sparkfun/SparkFun_RTK_Facet/Labels/SMA Cover - Blank/RTK Facet - SMA cover - Blank r2.pdf

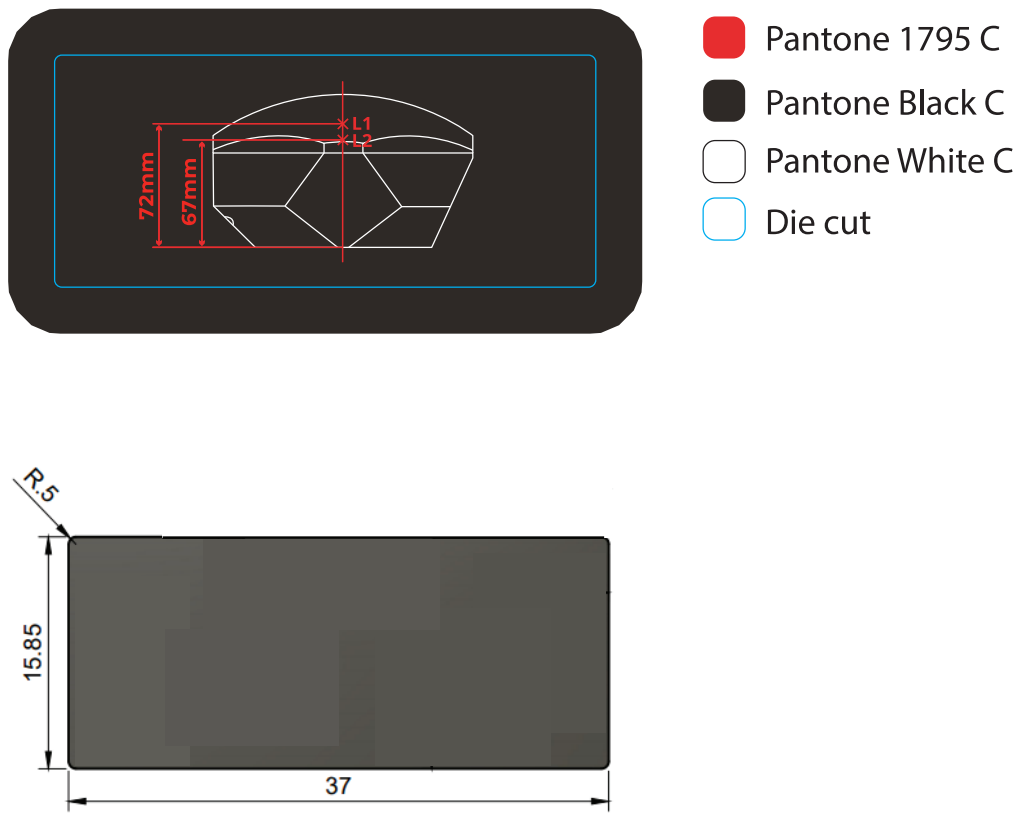
[picture p37: page 1]
