sparkfun/SparkFun_RTK_Facet/Labels/SMA Cover - Blank/RTK Facet - SMA cover - Blank LBand r1.pdf

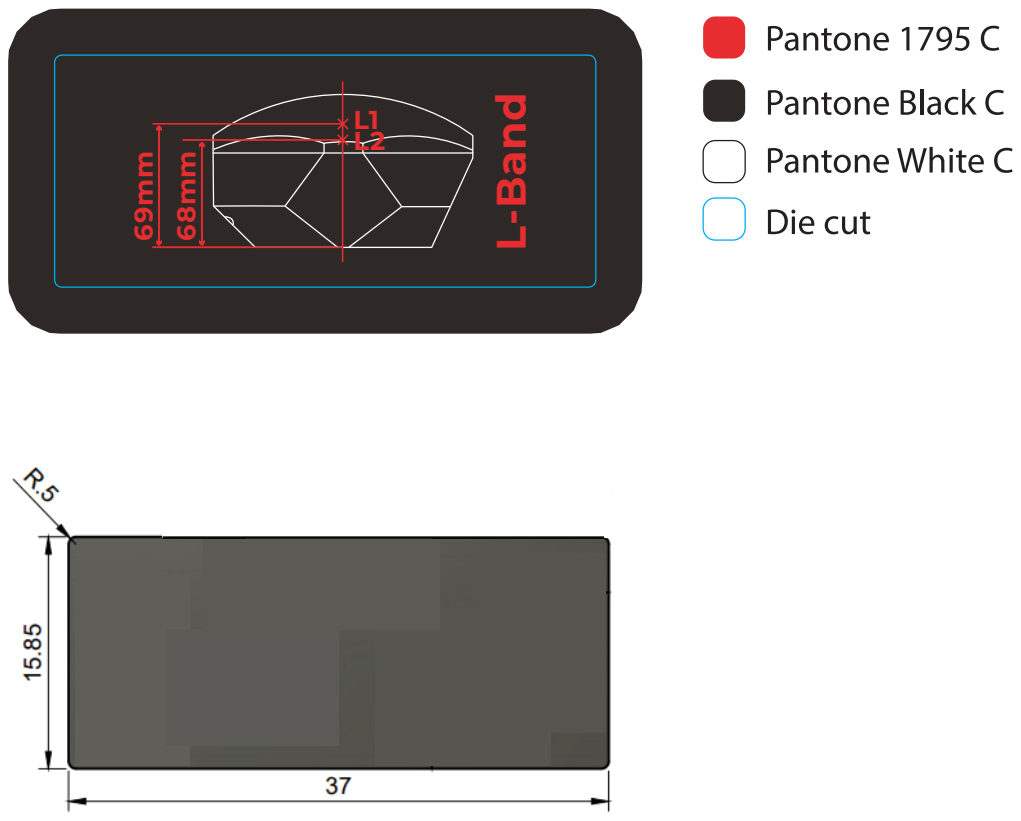
[picture p38: page 1]
L-Band
