sparkfun/SparkFun_RTK_Facet/Labels/SMA Cover - 915MHz/RTK Facet 915MHz Label (r1).pdf

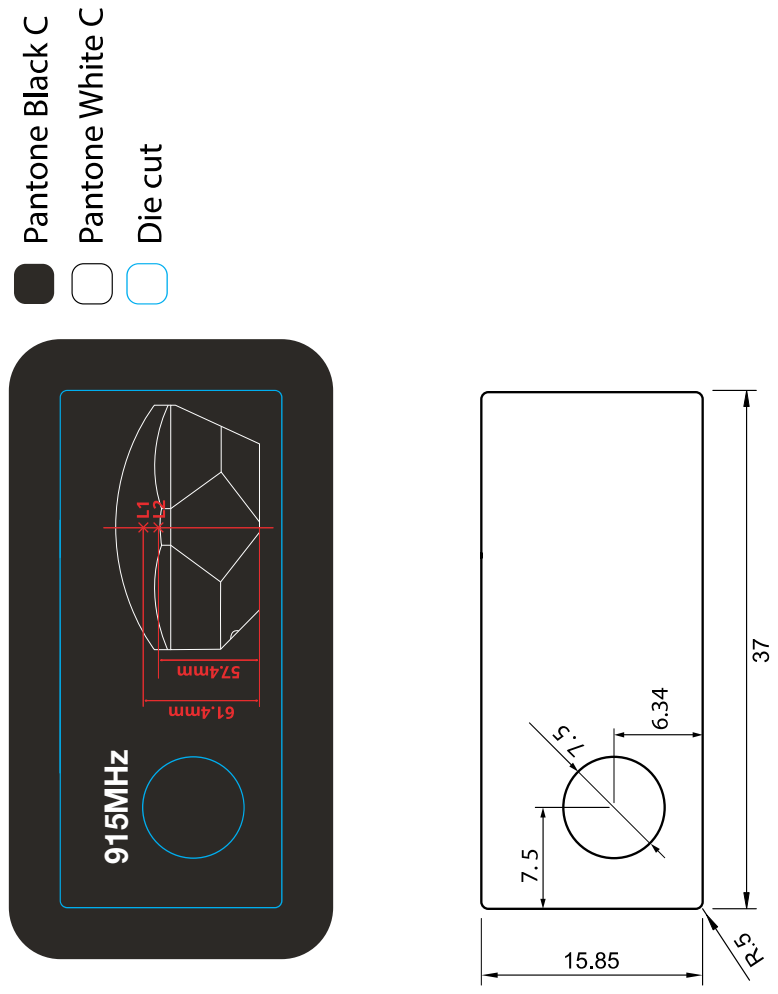
[picture p39: page 1]
915MHz
