sparkfun/SparkFun_RTK_Facet/Labels/SMA Cover - LTE/RTK Facet LTE Label.pdf

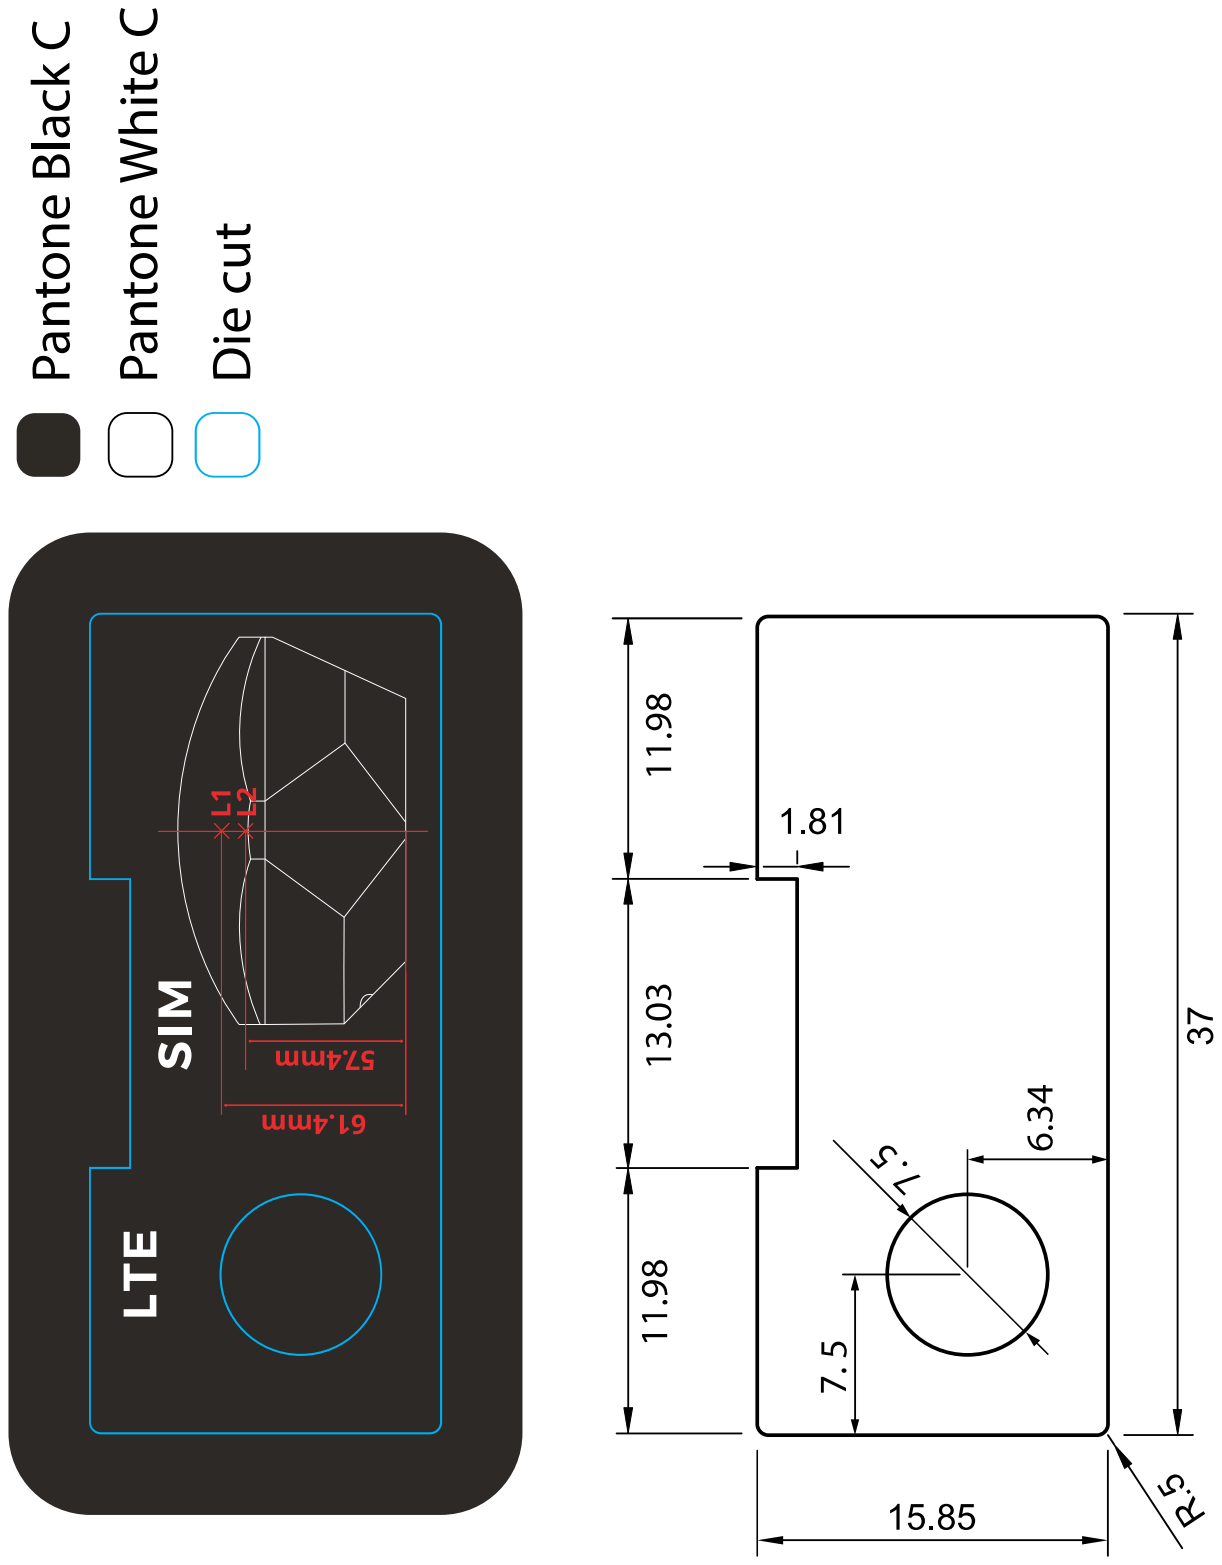
[picture p40: page 1]
