sparkfun/SparkFun_RTK_Facet/Labels/Display/RTK Facet Labels - All Outlines r2.pdf

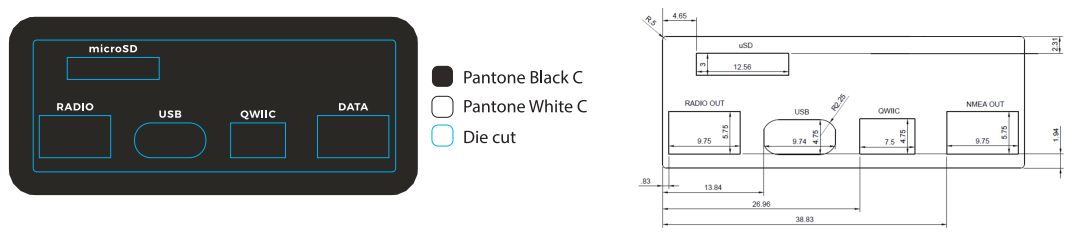
[picture p41: page 1]

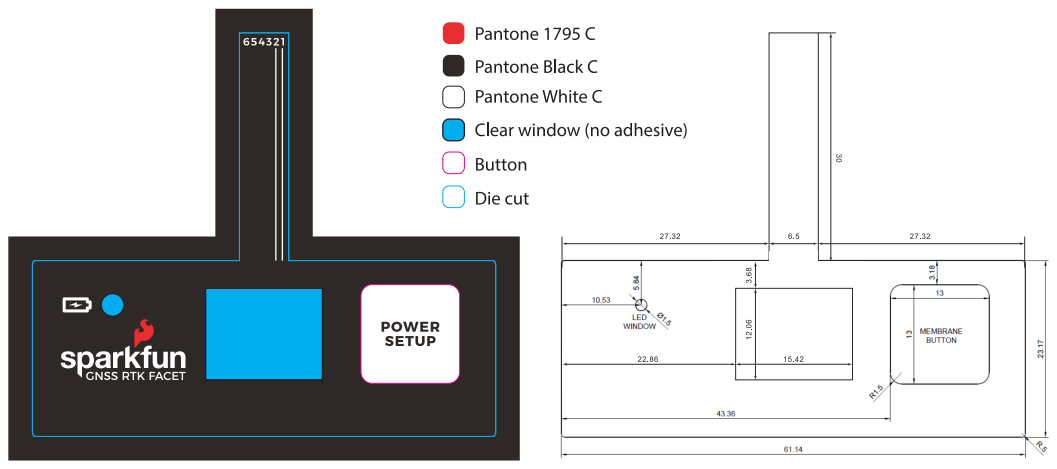
[picture p42: page 2]

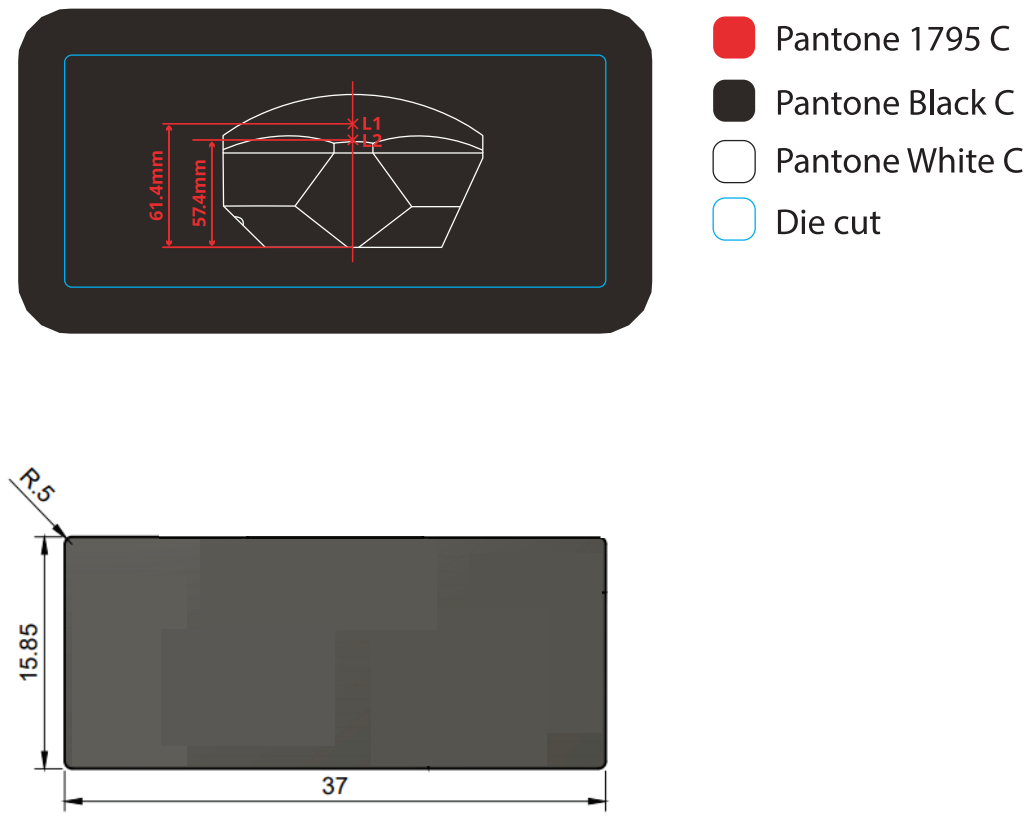
[picture p43: page 4]

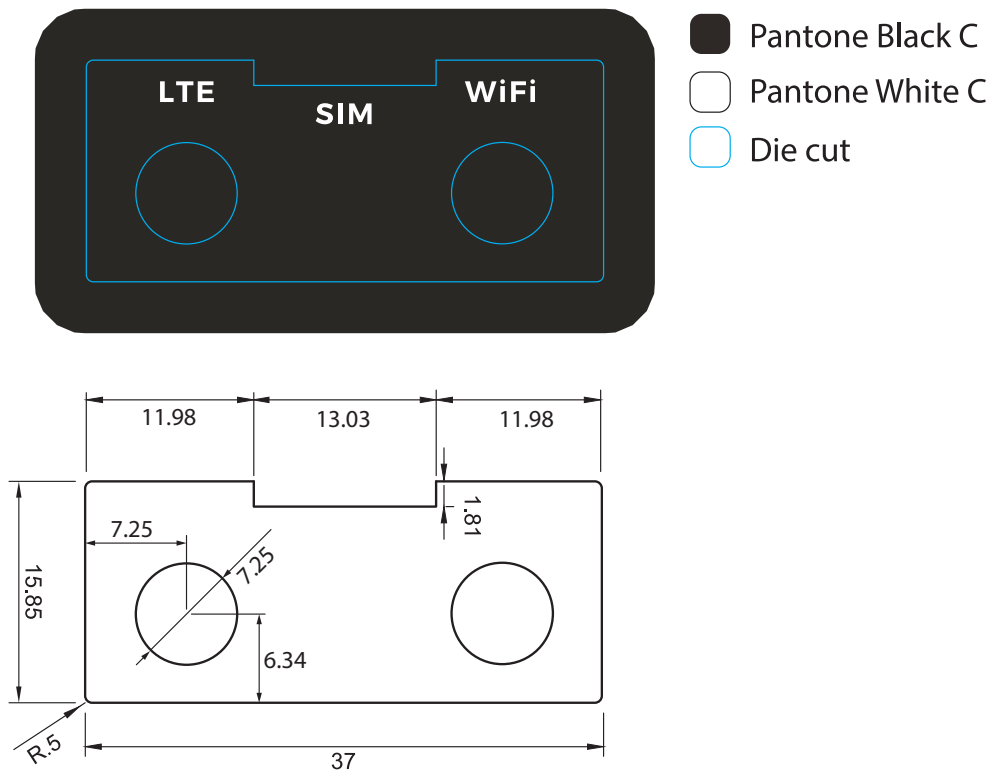
[picture p44: page 5]

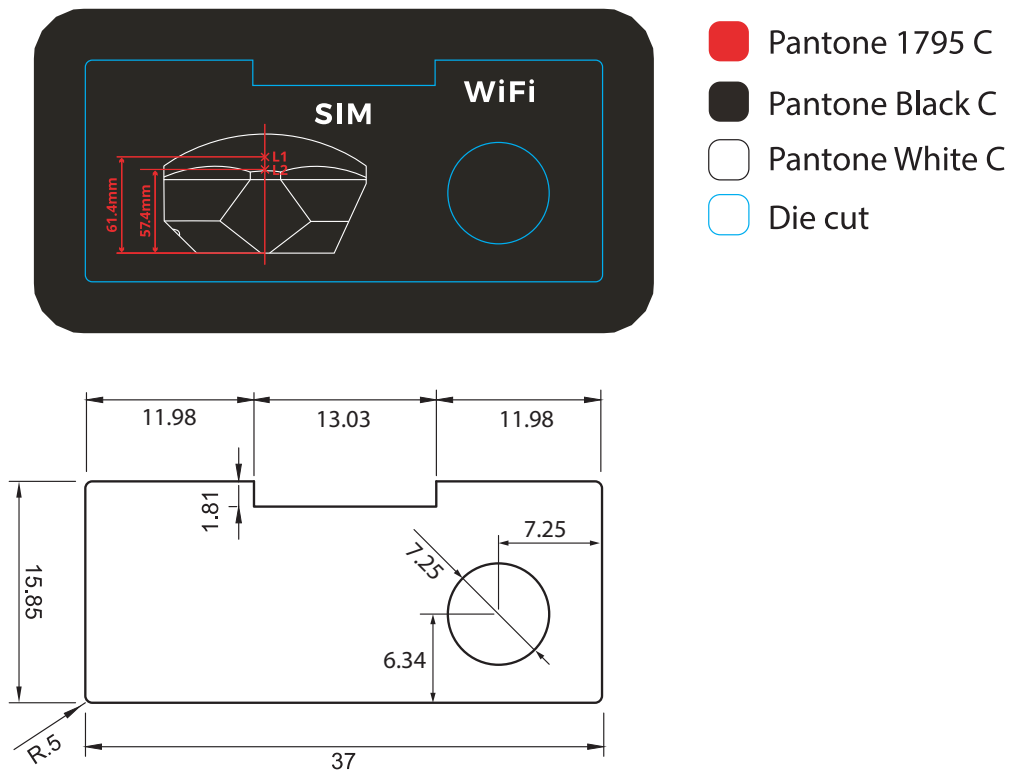
[picture p45: page 6]

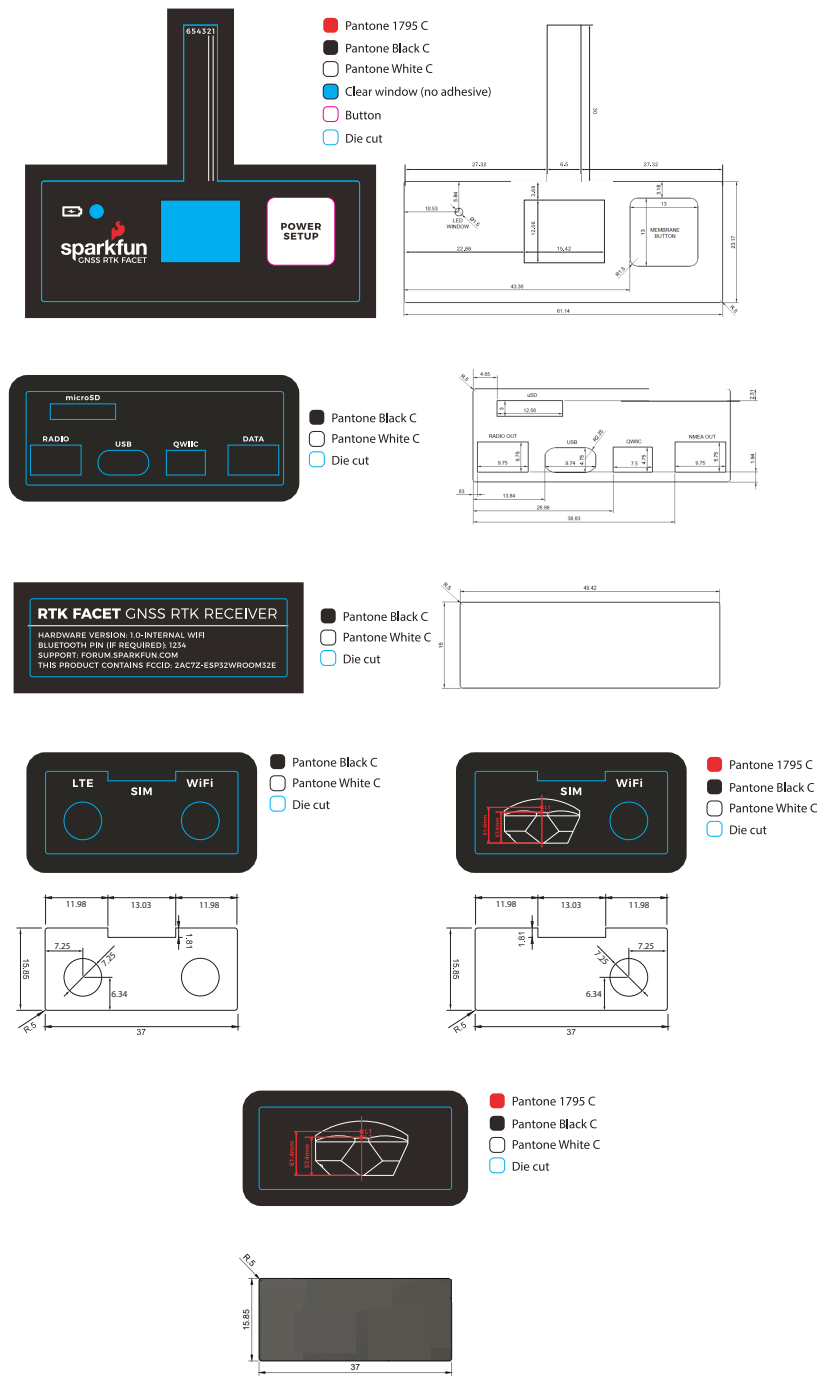
[picture p46: page 7]
