sparkfun/SparkFun_RTK_Facet/Labels/SMA Cover - WiFi+LTE/RTK Facet LTE+WiFi Label r2.pdf

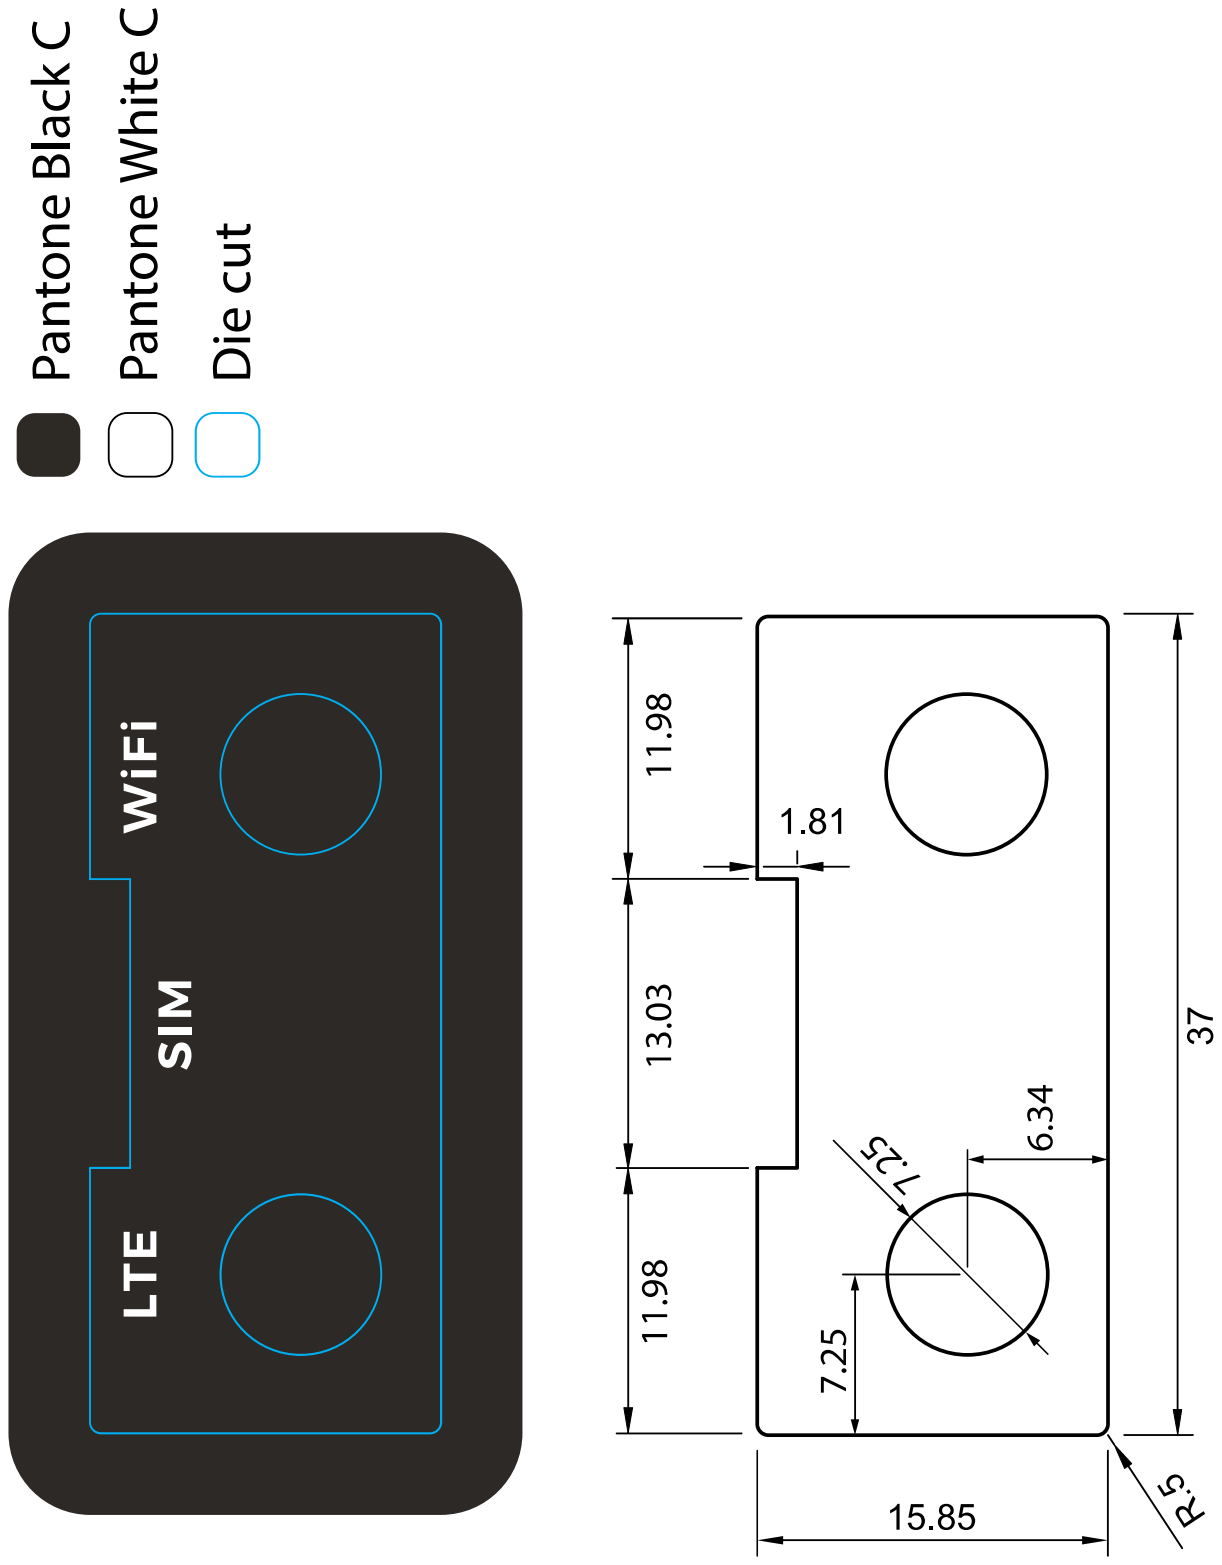
[picture p47: page 1]
