sparkfun/SparkFun_RTK_Facet/Labels/Display/RTK Facet - All Outlines r1.pdf

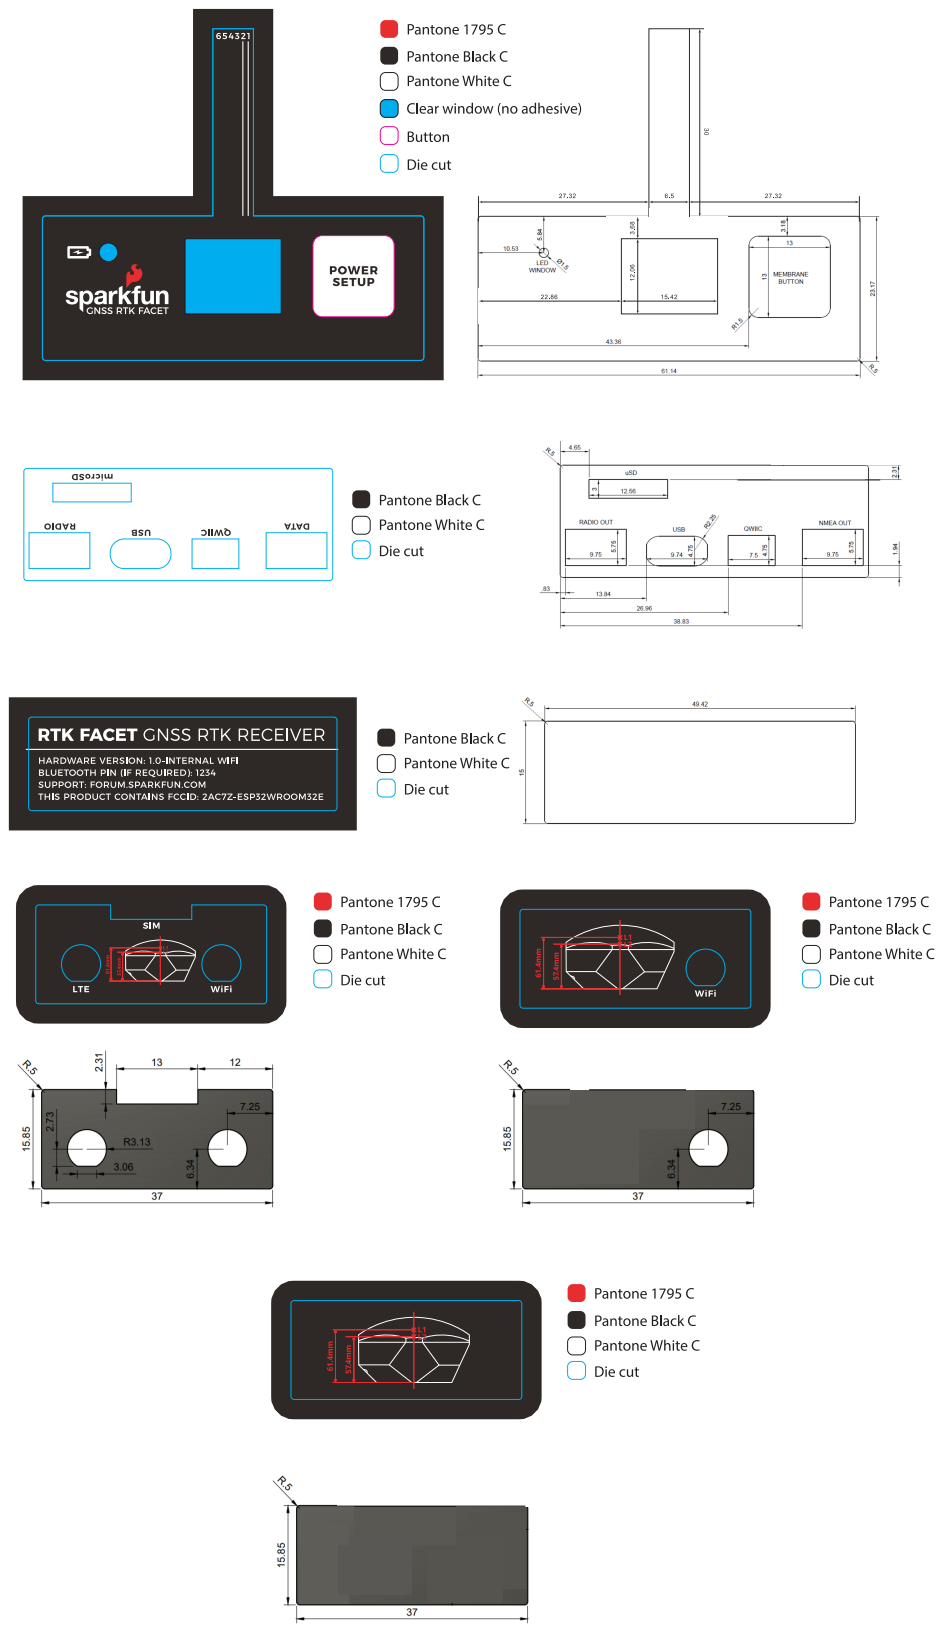
[picture p48: page 1]

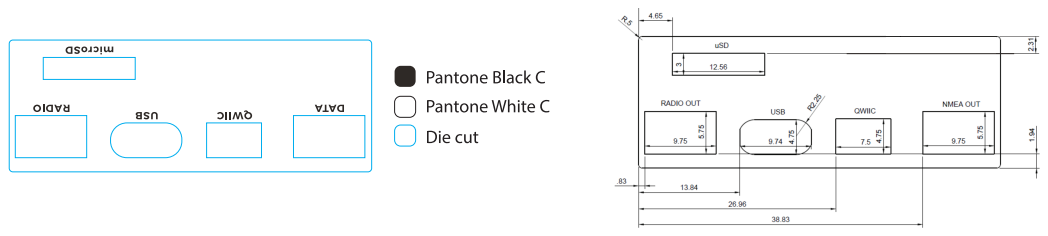
[picture p49: page 2]

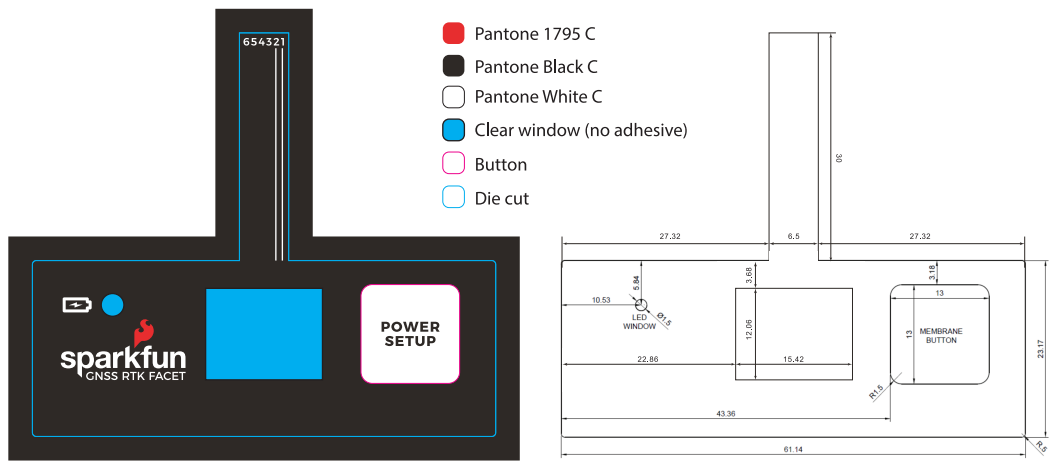
[picture p50: page 3]

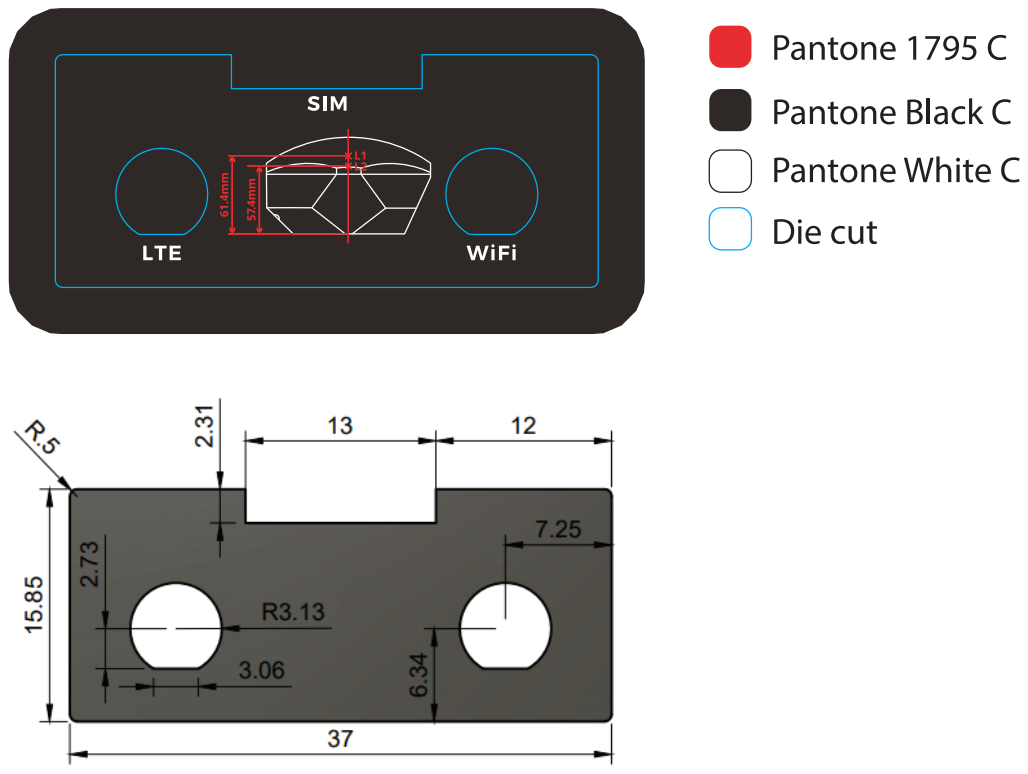
[picture p51: page 5]

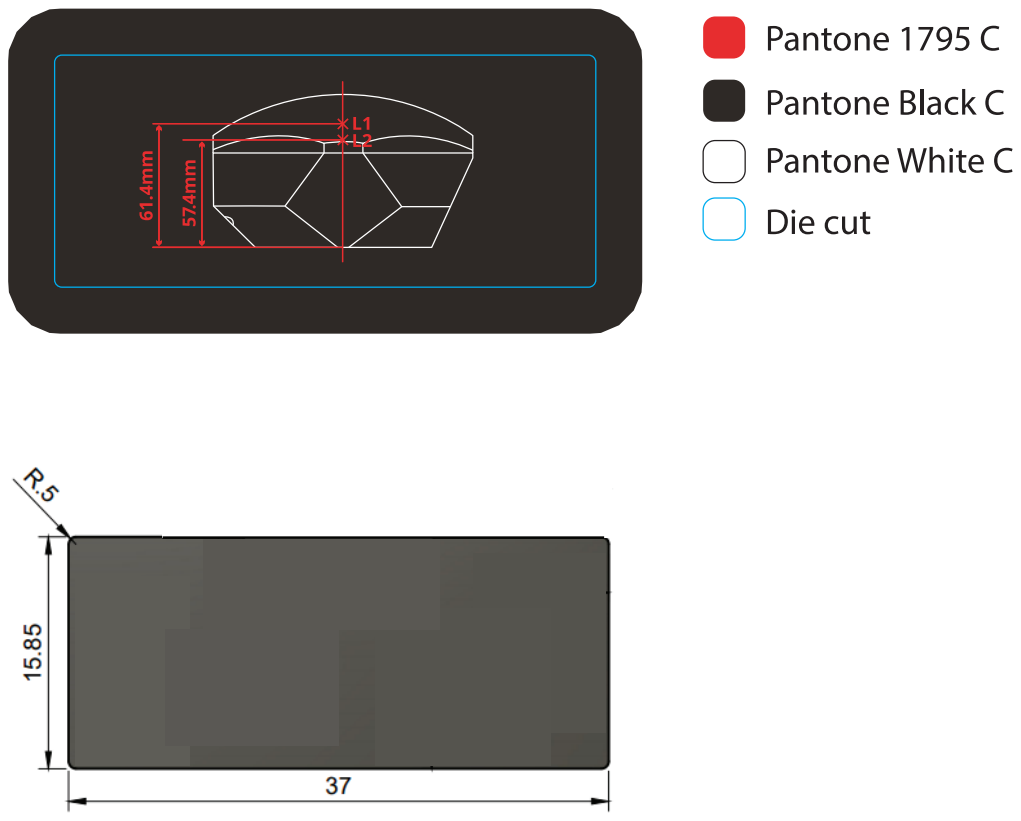
[picture p52: page 6]

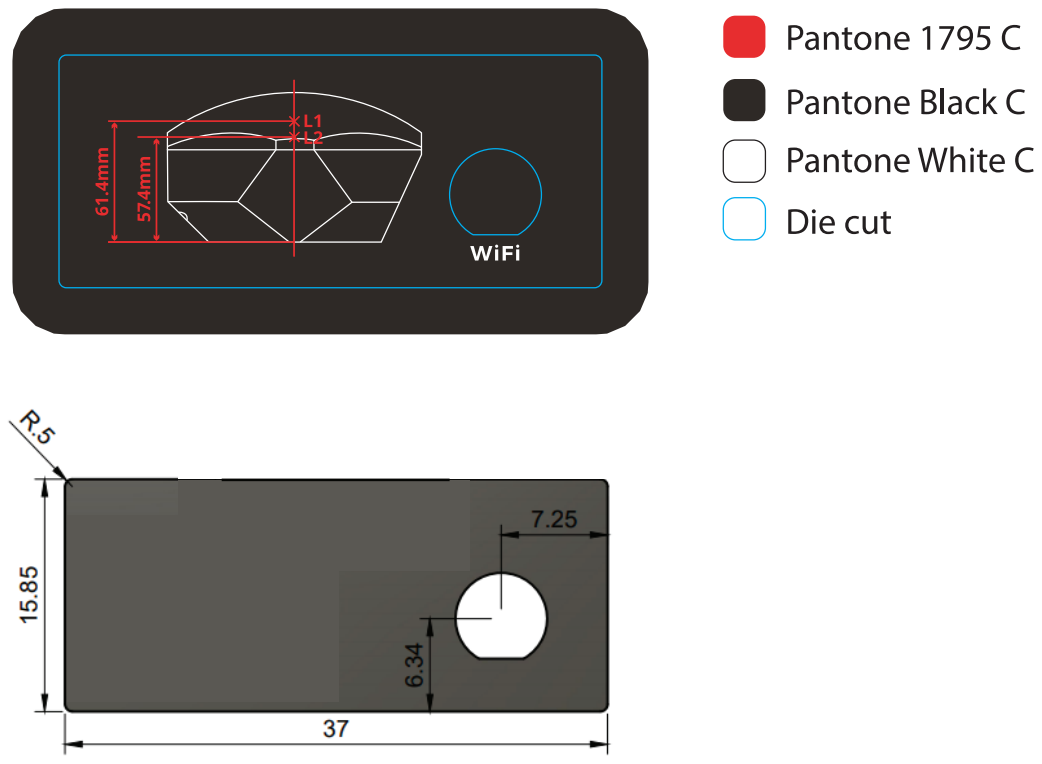
[picture p53: page 7]
