sparkfun/SparkFun_RTK_Facet/Labels/SMA Cover - Blank/RTK Facet - SMA cover - Blank r1.pdf

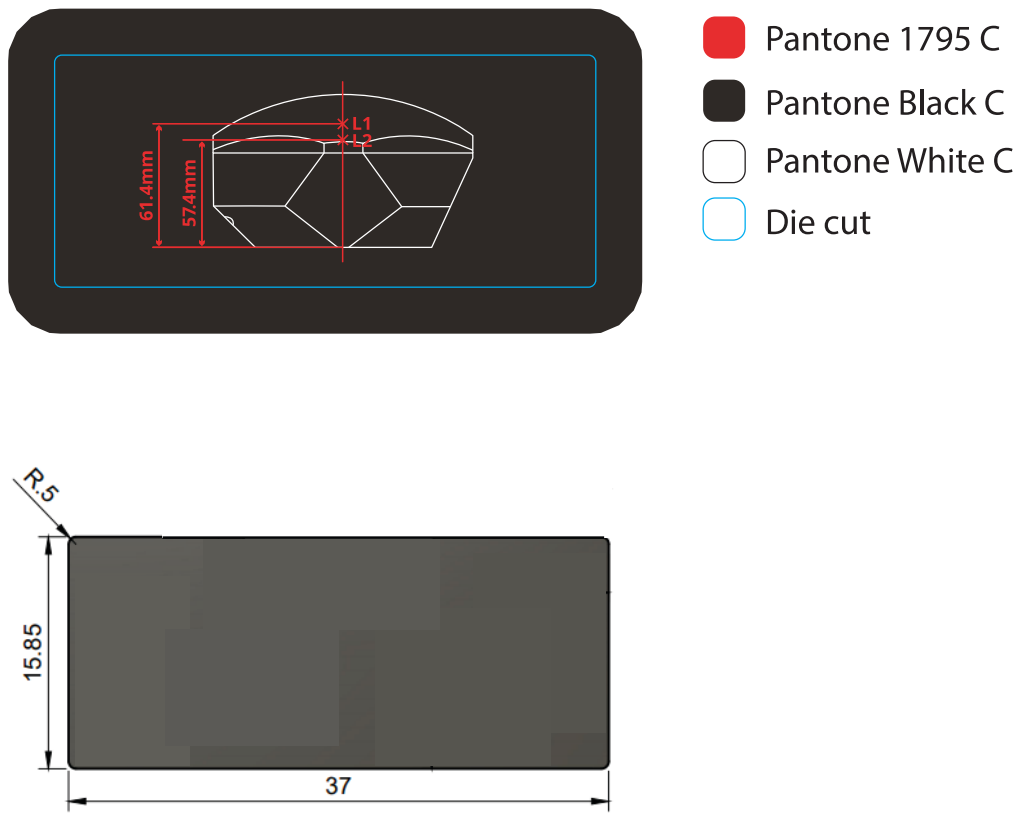
[picture p54: page 1]
