sparkfun/SparkFun_RTK_Facet/Labels/Display/Button Layout RTK Facet.sch

## EAGLE design Labels/Display/Button Layout RTK Facet.sch (2021-05-13)

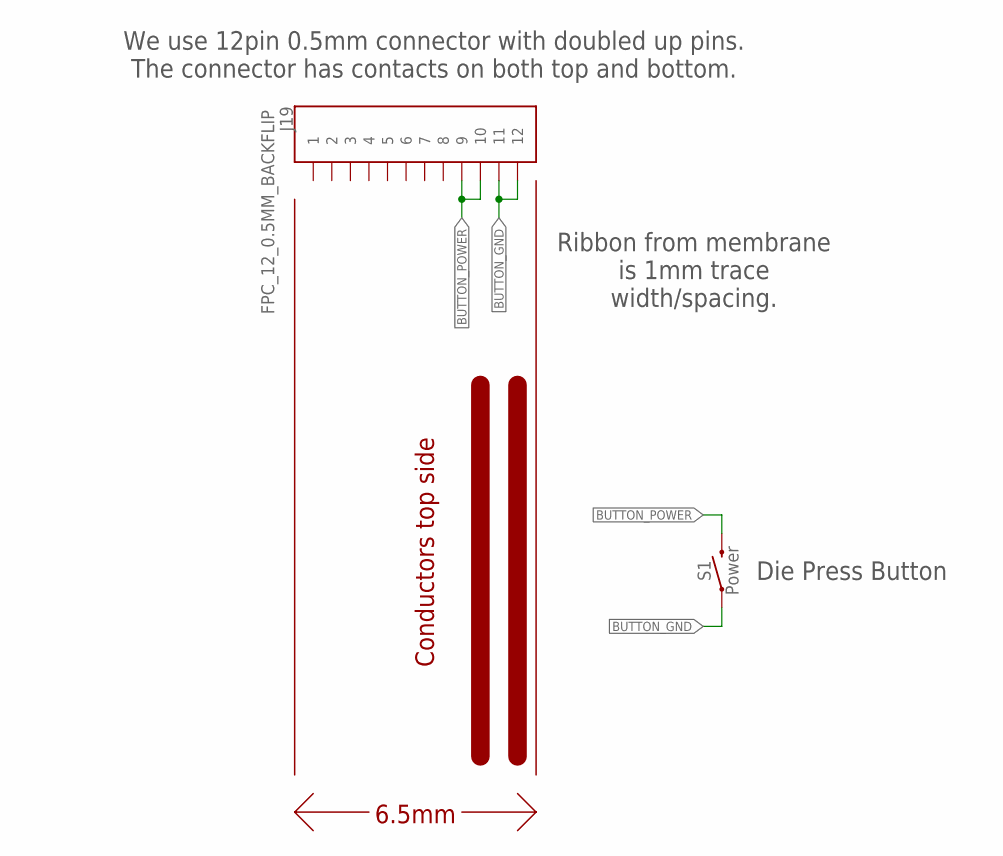
[picture p77: schematic Button Layout RTK Facet.sch]

Parts:
J19: FPC_12_0.5MM_BACKFLIP; FPC_12_DOUBLESIDED_BACKFLIP
S1: Power; TACTILE_SWITCH_PTH_6.0MM

Connections:
BUTTON_GND: J19.11, J19.12, S1.1
BUTTON_POWER: J19.9, J19.10, S1.3 (2)

Notes on the sheet:
Die Press Button
We use 12pin 0.5mm connector with doubled up pins. The connector has contacts on both top and bottom.
Conductors top side
6.5mm
Ribbon from membrane is 1mm trace width/spacing.
